CosmicPi/psutest/cosmicpiCWconverter.asc

C1: cap; 1µ
C2: cap; 10µ
C3: cap; 10µ
C4: cap; 10µ
C5: cap; 10µ
C6: cap; 10µ
C7: cap; 10µ
C8: cap; 10µ
C9: cap; 10µ
C10: cap; 10µ
C11: cap; 10µ
C12: cap; 10µ
C13: cap; 10µ
C14: cap; 10µ
C15: cap; 1µ
C20: cap; 1000p
C21: cap; 1000p
D1: diode; BAS16HM
D2: diode; BAS16HM
D3: diode; BAS16HM
D4: diode; BAS16HM
D5: diode; BAS16HM
D6: diode; BAS16HM
D7: diode; BAS16HM
D8: diode; BAS16HM
D9: diode; BAS16HM
D10: diode; BAS16HM
D11: diode; BAS16HM
D12: diode; BAS16HM
D13: diode; BAS16HM
R1: res; 1k
R2: res; 1
R3: res; 1Meg
R4: res; 1k
V1: voltage; PULSE(0 5 0 1u 1u 1u 100u)
Named nets: 0
.tran 0 1 0 1m
.lib BAS16GW.lib
